h3llb3nt/tty2rgbmatrix/desktop_frame/enclosure-front-no-panel.jpg

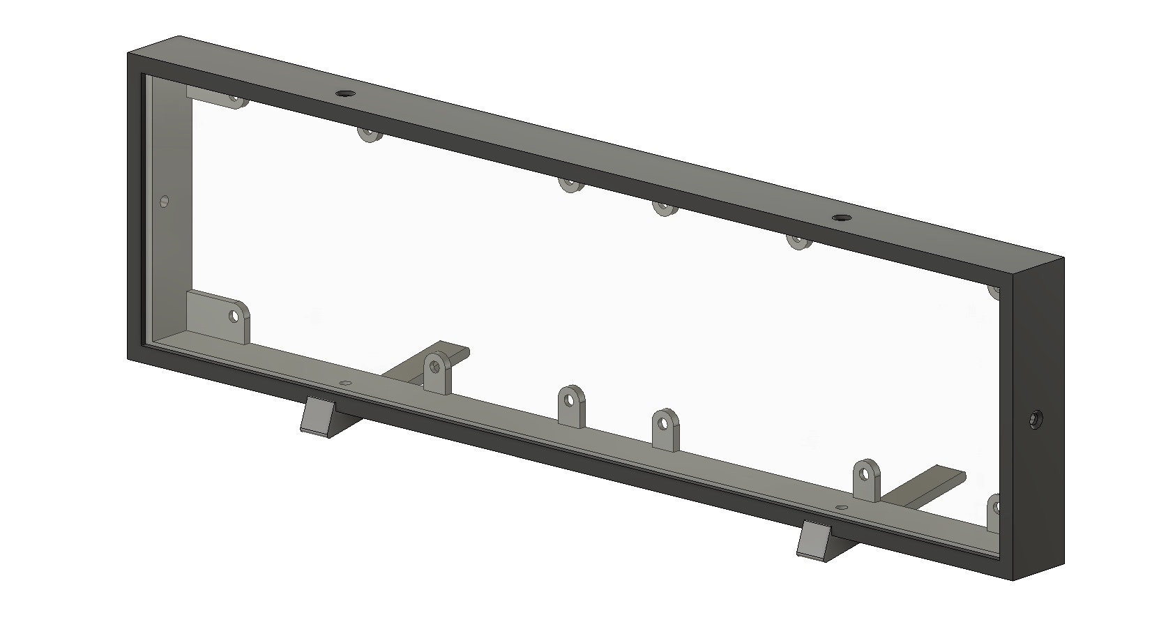
desktop_frame/enclosure-front-no-panel.jpg
