h3llb3nt/tty2rgbmatrix/desktop_frame/enclosure-rear.jpg

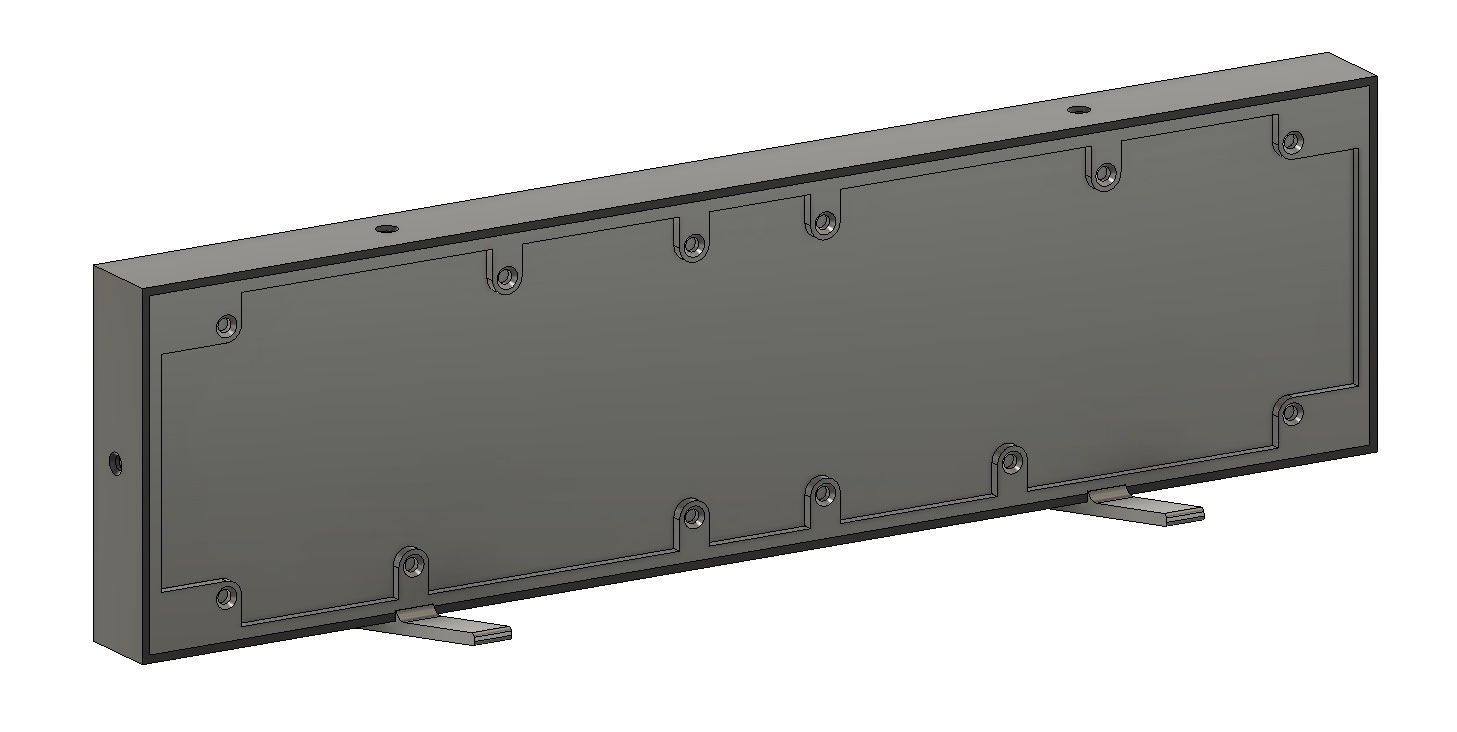
desktop_frame/enclosure-rear.jpg
