h3llb3nt/tty2rgbmatrix/desktop_frame/enclosure-underside.jpg

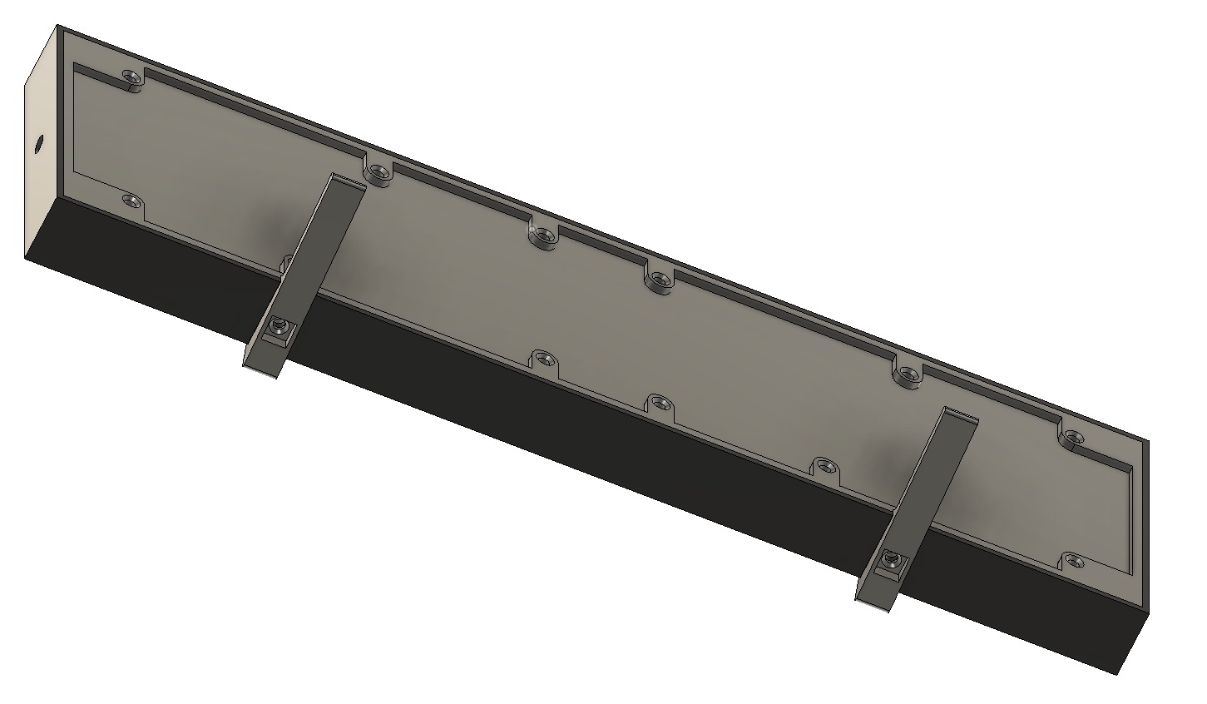
desktop_frame/enclosure-underside.jpg
