h3llb3nt/tty2rgbmatrix/docs/images/sdcard_long_pins.jpeg

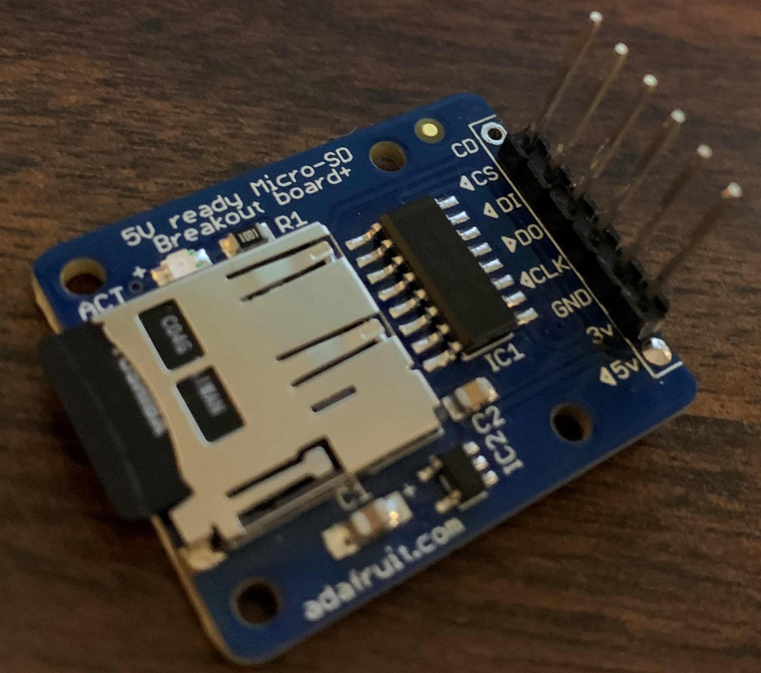
docs/images/sdcard_long_pins.jpeg
